GreenBotics/greenbotics-weather-station/src/GreenSkies_Node0/wifi.h

void getWifiData(){
  //ask user for data 
  /*ssid = getUserInput(ssidInitialized,"SSID");
  
  if(ssidInitialized){
    password = getUserInput(passwordInitialized,"password");
  }
  
  if(ssidInitialized && passwordInitialized && !wifiInitialized){
    Serial.print("Validated ssid: ");
    Serial.println(ssid.c_str());
    Serial.print("Pasword: ");
    Serial.println(password.c_str());

    wifiInitialized = true;
  }*/

  wifiInitialized = true;

}
